not-willem/BroAmp-EXG/imagesforreadme/image (1).png

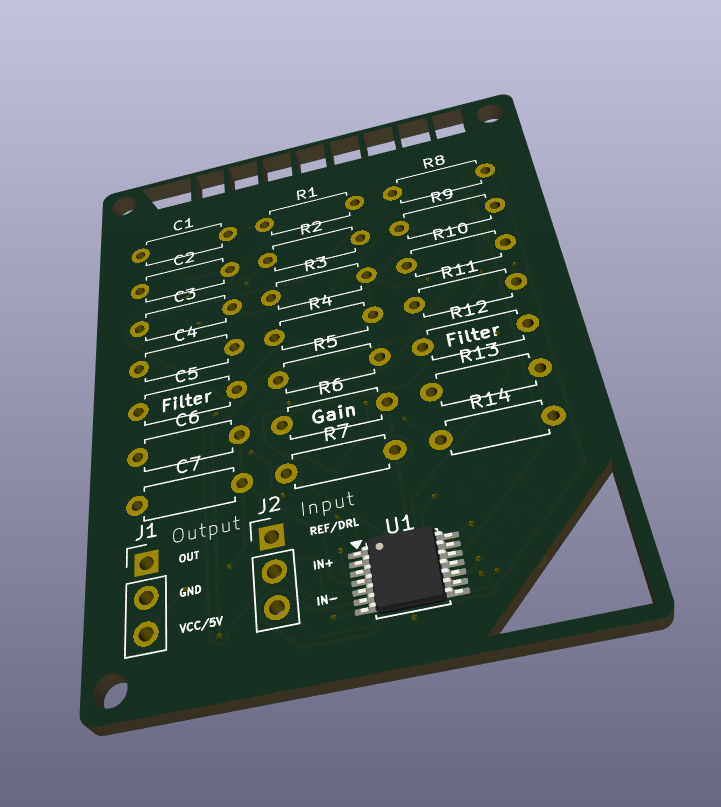
imagesforreadme/image (1).png
